totothekiller/weather-station/TeleInfo/shematics/TeleInfo_Node_PCB_circuit imprimé.png

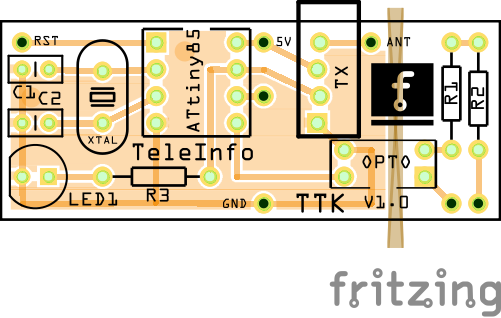
TeleInfo/shematics/TeleInfo_Node_PCB_circuit imprimé.png
