totothekiller/weather-station/Tests/ReadTemp/ReadTemp.ino

#include <OneWire.h>


// Read Temperature from DS18S20 with OneWire Protocol
//
// Warning : Parasite power is ON



OneWire  ds(10);  // on pin 10 (a 4.7K resistor is necessary)

void setup(void) {
  Serial.begin(9600);
}

void loop(void) {
  byte i;
  byte present = 0;
  byte type_s;
  byte data[12];
  byte addr[8];
  float celsius;
  
  if ( !ds.search(addr)) {
    Serial.println("No more addresses.");
    Serial.println();
    ds.reset_search();
    delay(250);
    return;
  }
  
  Serial.print("ROM =");
  for( i = 0; i < 8; i++) {
    Serial.write(' ');
    Serial.print(addr[i], HEX);
  }

  if (OneWire::crc8(addr, 7) != addr[7]) {
      Serial.println("CRC is not valid!");
      return;
  }
  Serial.println();
 
  // Check if chip is DS18B20
  if(addr[0]!=0x28)
  {
    Serial.println("Chip is not DS18B20");
      return;
  }
  
  
  ds.reset();
  ds.select(addr);
  ds.write(0x44,1);        // start conversion
  
  delay(1000);     // maybe 750ms is enough, maybe not
  // we might do a ds.depower() here, but the reset will take care of it.
  
  present = ds.reset();
  ds.select(addr);    
  ds.write(0xBE);         // Read Scratchpad

  Serial.print("  Data = ");
  Serial.print(present, HEX);
  Serial.print(" ");
  for ( i = 0; i < 9; i++) {           // we need 9 bytes
    data[i] = ds.read();
    Serial.print(data[i], HEX);
    Serial.print(" ");
  }
  Serial.print(" CRC=");
  Serial.print(OneWire::crc8(data, 8), HEX);
  Serial.println();

  // Convert the data to actual temperature
  float raw = (data[1] << 8) | data[0];
  celsius = raw / 16.0;

  Serial.print("  Temperature = ");
  Serial.print(celsius);
  Serial.println(" Celsius");
}
